amovitz/scann3d/zephyr-firmware/src/protocol.h

/*
 * protocol.h - Binary packet format shared across UDP and USB-serial streams.
 *
 * Wire layout (all multi-byte fields are little-endian):
 *
 *   [0x55 0xAA]   2 B  magic / frame-start
 *   [type]        1 B  packet type (enum scanner_pkt_type)
 *   [seq]         2 B  rolling sequence number (per type)
 *   [len]         2 B  payload length in bytes
 *   [payload]     N B  type-specific payload (see structs below)
 *   [crc16]       2 B  CRC-16/CCITT over bytes [type..payload]
 *
 * Total overhead: 9 bytes per frame.
 */

#ifndef SCANNER_PROTOCOL_H
#define SCANNER_PROTOCOL_H

#include <stdint.h>
#include <stddef.h>
#include <zephyr/data/json.h>

#ifdef __cplusplus
extern "C" {
#endif

/* ── Frame constants ──────────────────────────────────────────────────────── */
#define PROTO_MAGIC_0   0x55u
#define PROTO_MAGIC_1   0xAAu
#define PROTO_HDR_LEN   7u   /* magic(2)+type(1)+seq(2)+len(2) */
#define PROTO_FTR_LEN   2u   /* crc16(2) */
#define PROTO_OVERHEAD  (PROTO_HDR_LEN + PROTO_FTR_LEN)

/* ── Packet types ─────────────────────────────────────────────────────────── */
typedef enum __attribute__((packed)) {
    PKT_TOF   = 0x01,   /* VL53L8CX 8×8 ranging frame           */
    PKT_IMU0  = 0x02,   /* LSM6DSV main board (fixed)           */
    PKT_IMU1  = 0x03,   /* LSM6DSV tracker (detachable)         */
    PKT_SER0  = 0x04,   /* Servo 0                              */
    PKT_STATUS= 0xFF,   /* heartbeat / error flags              */
} scanner_pkt_type_t;

/* ── ToF payload (329 bytes) ──────────────────────────────────────────────── */
#define TOF_ZONES  64u   /* 8×8 */

typedef struct __attribute__((packed)) {
    uint32_t timestamp_ms;          /* k_uptime_get_32()                  */
    uint16_t distance_mm[TOF_ZONES];/* centre distance per zone, mm       */
    uint16_t sigma_mm[TOF_ZONES];   /* ranging sigma per zone, mm         */
    uint8_t  status[TOF_ZONES];     /* per-zone ranging status (ULD codes)*/
    uint8_t  nb_target_detected[TOF_ZONES]; /* targets per zone           */
} tof_payload_t;

/* ── IMU payload (20 bytes) ───────────────────────────────────────────────── */
typedef struct __attribute__((packed)) {
    uint32_t timestamp_ms;
    int16_t  accel_x;   /* raw 16-bit - scale = ±16 g / 32768             */
    int16_t  accel_y;
    int16_t  accel_z;
    int16_t  gyro_x;    /* raw 16-bit - scale = ±2000 dps / 32768         */
    int16_t  gyro_y;
    int16_t  gyro_z;
    int16_t  temp_raw;  /* LSM6DSV: (raw / 256) + 25 °C                   */
} imu_payload_t;

/* ── Status payload (4 bytes) ────────────────────────────────────────────── */
typedef struct __attribute__((packed)) {
    uint32_t timestamp_ms;
    uint8_t  tof_ok   : 1;
    uint8_t  imu0_ok  : 1;
    uint8_t  imu1_ok  : 1;
    uint8_t  wifi_ok  : 1;
    uint8_t  _rsvd    : 4;
} status_payload_t;

/* ── Servo payload (72 bytes) ────────────────────────────────────────────── */
typedef struct __attribute__((packed)) {
    uint32_t timestamp_ms;          /* k_uptime_get_32()                  */
    float    position;              /* float value from -1.0 to +1.0      */
    uint8_t  servo_num;             /* servo position                     */
} servo_payload_t;

#if defined(CONFIG_OUTPUT_JSON)

// FIXME: Buffer can be smaller
#define JSON_BUFFER_MAX  1024
#define FRAME_BUF_MAX    (JSON_BUFFER_MAX)

/* ── ToF JSON view ───────────────────────────────────────────────────────── */
typedef struct {
    uint32_t timestamp_ms;
    uint16_t distance_mm[TOF_ZONES];
    uint16_t sigma_mm[TOF_ZONES];
    uint8_t  status[TOF_ZONES];
    uint8_t  nb_target_detected[TOF_ZONES];
    size_t   distance_mm_len;
    size_t   sigma_mm_len;
    size_t   status_len;
    size_t   nb_target_detected_len;
} tof_json_t;

static const struct json_obj_descr tof_payload_descr[] = {
    JSON_OBJ_DESCR_PRIM(tof_json_t, timestamp_ms,        JSON_TOK_NUMBER),
    JSON_OBJ_DESCR_ARRAY(tof_json_t, distance_mm,        TOF_ZONES, distance_mm_len,        JSON_TOK_NUMBER),
    JSON_OBJ_DESCR_ARRAY(tof_json_t, sigma_mm,           TOF_ZONES, sigma_mm_len,           JSON_TOK_NUMBER),
    JSON_OBJ_DESCR_ARRAY(tof_json_t, status,             TOF_ZONES, status_len,             JSON_TOK_NUMBER),
    JSON_OBJ_DESCR_ARRAY(tof_json_t, nb_target_detected, TOF_ZONES, nb_target_detected_len, JSON_TOK_NUMBER),
};

/* ── IMU JSON view (shared for IMU0 and IMU1) ────────────────────────────── */
typedef struct {
    uint32_t timestamp_ms;
    int16_t  accel_x;   /* raw 16-bit - scale = ±16 g / 32768             */
    int16_t  accel_y;
    int16_t  accel_z;
    int16_t  gyro_x;    /* raw 16-bit - scale = ±2000 dps / 32768         */
    int16_t  gyro_y;
    int16_t  gyro_z;
    int16_t  temp_raw;  /* LSM6DSV: (raw / 256) + 25 °C                   */
    uint8_t  imu_num;
} imu_json_t;

static const struct json_obj_descr imu_payload_descr[] = {
    JSON_OBJ_DESCR_PRIM(imu_json_t, timestamp_ms, JSON_TOK_NUMBER),
    JSON_OBJ_DESCR_PRIM(imu_json_t, accel_x,      JSON_TOK_NUMBER),
    JSON_OBJ_DESCR_PRIM(imu_json_t, accel_y,      JSON_TOK_NUMBER),
    JSON_OBJ_DESCR_PRIM(imu_json_t, accel_z,      JSON_TOK_NUMBER),
    JSON_OBJ_DESCR_PRIM(imu_json_t, gyro_x,       JSON_TOK_NUMBER),
    JSON_OBJ_DESCR_PRIM(imu_json_t, gyro_y,       JSON_TOK_NUMBER),
    JSON_OBJ_DESCR_PRIM(imu_json_t, gyro_z,       JSON_TOK_NUMBER),
    JSON_OBJ_DESCR_PRIM(imu_json_t, temp_raw,     JSON_TOK_NUMBER),
    JSON_OBJ_DESCR_PRIM(imu_json_t, imu_num,      JSON_TOK_NUMBER),
};

/* ── Status JSON view ────────────────────────────────────────────────────── */
/* Bitfields can't be described directly — flatten into a wrapper */
typedef struct {
    uint32_t timestamp_ms;
    int      tof_ok;
    int      imu0_ok;
    int      imu1_ok;
    int      wifi_ok;
} status_json_t;

static const struct json_obj_descr status_payload_descr[] = {
    JSON_OBJ_DESCR_PRIM(status_json_t, timestamp_ms, JSON_TOK_NUMBER),
    JSON_OBJ_DESCR_PRIM(status_json_t, tof_ok,       JSON_TOK_NUMBER),
    JSON_OBJ_DESCR_PRIM(status_json_t, imu0_ok,      JSON_TOK_NUMBER),
    JSON_OBJ_DESCR_PRIM(status_json_t, imu1_ok,      JSON_TOK_NUMBER),
    JSON_OBJ_DESCR_PRIM(status_json_t, wifi_ok,      JSON_TOK_NUMBER),
};

/* ── Servo JSON view ─────────────────────────────────────────────────────── */
static const struct json_obj_descr servo_payload_descr[] = {
    JSON_OBJ_DESCR_PRIM(servo_payload_t, timestamp_ms, JSON_TOK_NUMBER),
    JSON_OBJ_DESCR_PRIM(servo_payload_t, position,     JSON_TOK_NUMBER),
    JSON_OBJ_DESCR_PRIM(servo_payload_t, servo_num,    JSON_TOK_NUMBER),
};

# else

/* ── Maximum serialised frame size ───────────────────────────────────────── */
#define FRAME_BUF_MAX    (PROTO_OVERHEAD + sizeof(tof_payload_t))

#endif /* CONFIG_OUTPUT_JSON */

/* ── Utility: build a complete frame into buf[], return total length ─────── */
uint16_t proto_encode(uint8_t *buf, size_t buf_size,
                      scanner_pkt_type_t type, uint16_t seq,
                      const void *payload, uint16_t payload_len);

#ifdef __cplusplus
}
#endif
#endif /* SCANNER_PROTOCOL_H */
